paulh002/ESP32vfo/ESP32vfo/FreeSansOblique24.c

/*******************************************************************************
 * Size: 24 px
 * Bpp: 1
 * Opts: 
 ******************************************************************************/

#ifdef LV_LVGL_H_INCLUDE_SIMPLE
#include "lvgl.h"
#else
#include "lvgl.h"
#endif

#ifndef FREESANSOBLIQUE24
#define FREESANSOBLIQUE24 1
#endif

#if FREESANSOBLIQUE24

/*-----------------
 *    BITMAPS
 *----------------*/

/*Store the image of the glyphs*/
static LV_ATTRIBUTE_LARGE_CONST const uint8_t glyph_bitmap[] = {
    /* U+0020 " " */
    0x0,

    /* U+002B "+" */
    0x1, 0x0, 0x30, 0x3, 0x0, 0x30, 0x2, 0xf,
    0xff, 0xff, 0xf0, 0x60, 0x6, 0x0, 0x40, 0xc,
    0x0, 0xc0,

    /* U+002C "," */
    0x77, 0x32, 0x2c,

    /* U+002D "-" */
    0x7f, 0xf0,

    /* U+002E "." */
    0xfc,

    /* U+0030 "0" */
    0x3, 0xc0, 0xfe, 0x1c, 0x71, 0x83, 0x30, 0x33,
    0x3, 0x70, 0x36, 0x3, 0x60, 0x36, 0x3, 0x60,
    0x7e, 0x6, 0xe0, 0x6c, 0xe, 0xe0, 0xc6, 0x1c,
    0x7f, 0x83, 0xf0, 0x8, 0x0,

    /* U+0031 "1" */
    0x6, 0xc, 0x33, 0xef, 0xc1, 0x83, 0xc, 0x18,
    0x30, 0x60, 0xc3, 0x6, 0xc, 0x18, 0x70, 0xc0,

    /* U+0032 "2" */
    0x3, 0xf0, 0x1f, 0xe0, 0xe1, 0x87, 0x7, 0x18,
    0xc, 0x60, 0x30, 0x1, 0x80, 0xe, 0x0, 0x70,
    0x7, 0x80, 0x3c, 0x3, 0xc0, 0x1c, 0x0, 0xe0,
    0x6, 0x0, 0x18, 0x0, 0xff, 0xe3, 0xff, 0x80,

    /* U+0033 "3" */
    0x7, 0xc0, 0xff, 0x1c, 0x73, 0x83, 0x30, 0x33,
    0x3, 0x0, 0x30, 0xe, 0x7, 0xc0, 0x7c, 0x0,
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
    0x0, 0xc0, 0x6, 0x0, 0xf8, 0x3, 0x80, 0x0,

    /* U+007A "z" */
    0x1f, 0xf1, 0xff, 0x0, 0x60, 0xc, 0x1, 0x80,
    0x30, 0x6, 0x0, 0xc0, 0x18, 0x3, 0x0, 0x60,
    0xf, 0xfc, 0xff, 0xc0
};


/*---------------------
 *  GLYPH DESCRIPTION
 *--------------------*/

static const lv_font_fmt_txt_glyph_dsc_t glyph_dsc[] = {
    {.bitmap_index = 0, .adv_w = 0, .box_w = 0, .box_h = 0, .ofs_x = 0, .ofs_y = 0} /* id = 0 reserved */,
    {.bitmap_index = 0, .adv_w = 107, .box_w = 1, .box_h = 1, .ofs_x = 0, .ofs_y = 0},
    {.bitmap_index = 1, .adv_w = 224, .box_w = 12, .box_h = 12, .ofs_x = 2, .ofs_y = 0},
    {.bitmap_index = 19, .adv_w = 107, .box_w = 4, .box_h = 6, .ofs_x = 1, .ofs_y = -4},
    {.bitmap_index = 22, .adv_w = 128, .box_w = 6, .box_h = 2, .ofs_x = 2, .ofs_y = 6},
    {.bitmap_index = 24, .adv_w = 107, .box_w = 3, .box_h = 2, .ofs_x = 2, .ofs_y = 0},
    {.bitmap_index = 25, .adv_w = 214, .box_w = 12, .box_h = 19, .ofs_x = 2, .ofs_y = -1},
    {.bitmap_index = 54, .adv_w = 214, .box_w = 7, .box_h = 18, .ofs_x = 5, .ofs_y = 0},
    {.bitmap_index = 70, .adv_w = 214, .box_w = 14, .box_h = 18, .ofs_x = 1, .ofs_y = 0},
    {.bitmap_index = 102, .adv_w = 214, .box_w = 12, .box_h = 19, .ofs_x = 2, .ofs_y = -1},
    {.bitmap_index = 131, .adv_w = 214, .box_w = 12, .box_h = 18, .ofs_x = 2, .ofs_y = 0},
    {.bitmap_index = 158, .adv_w = 214, .box_w = 13, .box_h = 19, .ofs_x = 2, .ofs_y = -1},
    {.bitmap_index = 189, .adv_w = 214, .box_w = 13, .box_h = 19, .ofs_x = 2, .ofs_y = -1},
    {.bitmap_index = 220, .adv_w = 214, .box_w = 13, .box_h = 18, .ofs_x = 3, .ofs_y = 0},
    {.bitmap_index = 250, .adv_w = 214, .box_w = 13, .box_h = 19, .ofs_x = 2, .ofs_y = -1},
    {.bitmap_index = 281, .adv_w = 214, .box_w = 12, .box_h = 19, .ofs_x = 2, .ofs_y = -1},
    {.bitmap_index = 310, .adv_w = 224, .box_w = 13, .box_h = 11, .ofs_x = 2, .ofs_y = 0},
    {.bitmap_index = 328, .adv_w = 224, .box_w = 13, .box_h = 11, .ofs_x = 1, .ofs_y = 0},
    {.bitmap_index = 346, .adv_w = 214, .box_w = 11, .box_h = 18, .ofs_x = 4, .ofs_y = 0},
    {.bitmap_index = 371, .adv_w = 256, .box_w = 16, .box_h = 18, .ofs_x = 0, .ofs_y = 0},
    {.bitmap_index = 407, .adv_w = 256, .box_w = 15, .box_h = 18, .ofs_x = 2, .ofs_y = 0},
    {.bitmap_index = 441, .adv_w = 277, .box_w = 15, .box_h = 19, .ofs_x = 3, .ofs_y = -1},
    {.bitmap_index = 477, .adv_w = 277, .box_w = 16, .box_h = 18, .ofs_x = 2, .ofs_y = 0},
    {.bitmap_index = 513, .adv_w = 256, .box_w = 16, .box_h = 18, .ofs_x = 2, .ofs_y = 0},
    {.bitmap_index = 549, .adv_w = 235, .box_w = 16, .box_h = 18, .ofs_x = 2, .ofs_y = 0},
    {.bitmap_index = 585, .adv_w = 299, .box_w = 16, .box_h = 19, .ofs_x = 3, .ofs_y = -1},
    {.bitmap_index = 623, .adv_w = 277, .box_w = 17, .box_h = 18, .ofs_x = 2, .ofs_y = 0},
    {.bitmap_index = 662, .adv_w = 107, .box_w = 6, .box_h = 18, .ofs_x = 2, .ofs_y = 0},
    {.bitmap_index = 676, .adv_w = 192, .box_w = 13, .box_h = 19, .ofs_x = 1, .ofs_y = -1},
    {.bitmap_index = 707, .adv_w = 256, .box_w = 18, .box_h = 18, .ofs_x = 2, .ofs_y = 0},
    {.bitmap_index = 748, .adv_w = 214, .box_w = 11, .box_h = 18, .ofs_x = 2, .ofs_y = 0},
    {.bitmap_index = 773, .adv_w = 320, .box_w = 20, .box_h = 18, .ofs_x = 2, .ofs_y = 0},
    {.bitmap_index = 818, .adv_w = 277, .box_w = 17, .box_h = 18, .ofs_x = 2, .ofs_y = 0},
    {.bitmap_index = 857, .adv_w = 299, .box_w = 18, .box_h = 19, .ofs_x = 2, .ofs_y = -1},
    {.bitmap_index = 900, .adv_w = 256, .box_w = 16, .box_h = 18, .ofs_x = 2, .ofs_y = 0},
    {.bitmap_index = 936, .adv_w = 299, .box_w = 18, .box_h = 19, .ofs_x = 2, .ofs_y = -1},
    {.bitmap_index = 979, .adv_w = 277, .box_w = 16, .box_h = 18, .ofs_x = 2, .ofs_y = 0},
    {.bitmap_index = 1015, .adv_w = 256, .box_w = 15, .box_h = 19, .ofs_x = 2, .ofs_y = -1},
    {.bitmap_index = 1051, .adv_w = 235, .box_w = 14, .box_h = 18, .ofs_x = 4, .ofs_y = 0},
    {.bitmap_index = 1083, .adv_w = 277, .box_w = 16, .box_h = 19, .ofs_x = 3, .ofs_y = -1},
    {.bitmap_index = 1121, .adv_w = 256, .box_w = 15, .box_h = 18, .ofs_x = 4, .ofs_y = 0},
    {.bitmap_index = 1155, .adv_w = 362, .box_w = 22, .box_h = 18, .ofs_x = 4, .ofs_y = 0},
    {.bitmap_index = 1205, .adv_w = 256, .box_w = 18, .box_h = 18, .ofs_x = 1, .ofs_y = 0},
    {.bitmap_index = 1246, .adv_w = 256, .box_w = 16, .box_h = 18, .ofs_x = 4, .ofs_y = 0},
    {.bitmap_index = 1282, .adv_w = 235, .box_w = 17, .box_h = 18, .ofs_x = 1, .ofs_y = 0},
    {.bitmap_index = 1321, .adv_w = 107, .box_w = 10, .box_h = 23, .ofs_x = 0, .ofs_y = -5},
    {.bitmap_index = 1350, .adv_w = 107, .box_w = 10, .box_h = 23, .ofs_x = -1, .ofs_y = -5},
    {.bitmap_index = 1379, .adv_w = 214, .box_w = 12, .box_h = 14, .ofs_x = 2, .ofs_y = -1},
    {.bitmap_index = 1400, .adv_w = 214, .box_w = 13, .box_h = 19, .ofs_x = 1, .ofs_y = -1},
    {.bitmap_index = 1431, .adv_w = 192, .box_w = 11, .box_h = 14, .ofs_x = 2, .ofs_y = -1},
    {.bitmap_index = 1451, .adv_w = 214, .box_w = 14, .box_h = 19, .ofs_x = 2, .ofs_y = -1},
    {.bitmap_index = 1485, .adv_w = 214, .box_w = 12, .box_h = 14, .ofs_x = 2, .ofs_y = -1},
    {.bitmap_index = 1506, .adv_w = 107, .box_w = 8, .box_h = 18, .ofs_x = 2, .ofs_y = 0},
    {.bitmap_index = 1524, .adv_w = 214, .box_w = 13, .box_h = 18, .ofs_x = 1, .ofs_y = -5},
    {.bitmap_index = 1554, .adv_w = 214, .box_w = 12, .box_h = 18, .ofs_x = 2, .ofs_y = 0},
    {.bitmap_index = 1581, .adv_w = 85, .box_w = 5, .box_h = 18, .ofs_x = 2, .ofs_y = 0},
    {.bitmap_index = 1593, .adv_w = 85, .box_w = 9, .box_h = 23, .ofs_x = -2, .ofs_y = -5},
    {.bitmap_index = 1619, .adv_w = 192, .box_w = 13, .box_h = 18, .ofs_x = 1, .ofs_y = 0},
    {.bitmap_index = 1649, .adv_w = 85, .box_w = 5, .box_h = 18, .ofs_x = 2, .ofs_y = 0},
    {.bitmap_index = 1661, .adv_w = 320, .box_w = 18, .box_h = 13, .ofs_x = 2, .ofs_y = 0},
    {.bitmap_index = 1691, .adv_w = 214, .box_w = 12, .box_h = 13, .ofs_x = 2, .ofs_y = 0},
    {.bitmap_index = 1711, .adv_w = 214, .box_w = 12, .box_h = 14, .ofs_x = 2, .ofs_y = -1},
    {.bitmap_index = 1732, .adv_w = 214, .box_w = 14, .box_h = 18, .ofs_x = 0, .ofs_y = -5},
    {.bitmap_index = 1764, .adv_w = 214, .box_w = 13, .box_h = 18, .ofs_x = 2, .ofs_y = -5},
    {.bitmap_index = 1794, .adv_w = 128, .box_w = 8, .box_h = 13, .ofs_x = 2, .ofs_y = 0},
    {.bitmap_index = 1807, .adv_w = 192, .box_w = 11, .box_h = 14, .ofs_x = 1, .ofs_y = -1},
    {.bitmap_index = 1827, .adv_w = 107, .box_w = 7, .box_h = 17, .ofs_x = 2, .ofs_y = -1},
    {.bitmap_index = 1842, .adv_w = 214, .box_w = 12, .box_h = 14, .ofs_x = 2, .ofs_y = -1},
    {.bitmap_index = 1863, .adv_w = 192, .box_w = 11, .box_h = 13, .ofs_x = 3, .ofs_y = 0},
    {.bitmap_index = 1881, .adv_w = 277, .box_w = 17, .box_h = 13, .ofs_x = 3, .ofs_y = 0},
    {.bitmap_index = 1909, .adv_w = 192, .box_w = 14, .box_h = 13, .ofs_x = 0, .ofs_y = 0},
    {.bitmap_index = 1932, .adv_w = 192, .box_w = 14, .box_h = 18, .ofs_x = 0, .ofs_y = -5},
    {.bitmap_index = 1964, .adv_w = 192, .box_w = 12, .box_h = 13, .ofs_x = 1, .ofs_y = 0}
};

/*---------------------
 *  CHARACTER MAPPING
 *--------------------*/

static const uint8_t glyph_id_ofs_list_0[] = {
    0, 0, 0, 0, 0, 0, 0, 0,
    0, 0, 0, 1, 2, 3, 4, 0,
    5, 6, 7, 8, 9, 10, 11, 12,
    13, 14, 0, 0, 15, 0, 16, 17,
    0, 18, 19, 20, 21, 22, 23, 24,
    25, 26, 27, 28, 29, 30, 31, 32,
    33, 34, 35, 36, 37, 38, 39, 40,
    41, 42, 43, 44, 0, 45
};

/*Collect the unicode lists and glyph_id offsets*/
static const lv_font_fmt_txt_cmap_t cmaps[] =
{
    {
        .range_start = 32, .range_length = 62, .glyph_id_start = 1,
        .unicode_list = NULL, .glyph_id_ofs_list = glyph_id_ofs_list_0, .list_length = 62, .type = LV_FONT_FMT_TXT_CMAP_FORMAT0_FULL
    },
    {
        .range_start = 97, .range_length = 26, .glyph_id_start = 47,
        .unicode_list = NULL, .glyph_id_ofs_list = NULL, .list_length = 0, .type = LV_FONT_FMT_TXT_CMAP_FORMAT0_TINY
    }
};

/*-----------------
 *    KERNING
 *----------------*/


/*Map glyph_ids to kern left classes*/
static const uint8_t kern_left_class_mapping[] =
{
    0, 0, 0, 0, 1, 0, 0, 0,
    0, 0, 0, 0, 0, 0, 0, 0,
    0, 0, 0, 2, 3, 4, 4, 5,
    6, 4, 0, 0, 7, 8, 9, 0,
    0, 10, 11, 10, 12, 13, 14, 0,
    15, 15, 8, 15, 8, 0, 0, 16,
    17, 17, 0, 17, 18, 0, 19, 0,
    0, 20, 0, 19, 19, 17, 17, 0,
    21, 22, 23, 0, 24, 24, 20, 24,
    25
};

/*Map glyph_ids to kern right classes*/
static const uint8_t kern_right_class_mapping[] =
{
    0, 0, 0, 0, 0, 0, 0, 0,
    0, 0, 0, 0, 0, 0, 0, 0,
    0, 0, 0, 1, 0, 2, 0, 0,
    0, 2, 0, 0, 3, 0, 0, 0,
    0, 2, 0, 2, 0, 4, 5, 0,
    6, 6, 7, 6, 7, 0, 0, 8,
    0, 9, 9, 9, 10, 8, 0, 0,
    11, 0, 0, 12, 12, 9, 13, 9,
    14, 15, 10, 16, 17, 17, 18, 17,
    12
};

/*Kern values between classes*/
static const int8_t kern_class_values[] =
{
    -23, -8, -8, -23, -19, -23, -23, -15,
    0, -19, -12, -15, -15, -15, -19, -15,
    -23, -23, 0, -15, 0, -12, -15, -23,
    -4, -8, -8, -12, 0, -12, -8, -12,
    -8, -10, -12, 0, -12, -12, 0, -8,
    -19, -19, -19, -4, 0, -4, -8, -12,
    -4, -8, -4, -8, -12, -12, -15, -8,
    0, -4, -15, -19, -15, -8, 0, -8,
    -12, -12, -8, -8, -8, -12, -4, -12,
    -12, -15, -8, -19, -8, -19, -12, -12,
    -12, -12, -12, -15, -8, -12, -8, -17,
    -15, -12, -15, -12, -12, -15, 0, -8,
    -12, -12, -12, -8, -8, -19, -12, -15,
    -15, -19, -4, -15, -12, -12, 0, -12,
    0, -19, -19, -12, -8, 0, -8, -15,
    -8, -12, -8, -15, -12, -19, 0, -19,
    0, -19, 0, 0, 0, -12, -15, -12,
    -4, -15, -12, -15, -8, -15, -12, -8,
    0, -15, 0, -15, -15, -23, 0, -8,
    -12, -12, -4, -15, 0, -12, -8, -15,
    -15, 0, -12, 0, 0, -8, -15, -15,
    -19, -8, 0, 0, 0, -8, -4, -8,
    0, -6, 0, 0, -23, -8, -15, -12,
    -12, -15, -23, -19, -15, 0, 0, -15,
    -8, -12, -12, -15, 0, -15, -4, -4,
    0, -8, -8, -19, -8, -4, -4, 0,
    -4, -4, -4, -8, -4, -15, -4, 0,
    -12, -8, 0, -4, -15, -19, -19, 0,
    0, -4, -4, -8, -4, -8, 0, -10,
    -8, -15, -19, -15, -15, -15, 0, -4,
    -15, -15, -15, -8, 0, -15, -12, -15,
    -15, -15, -8, -12, -23, -19, -12, -19,
    0, 0, -12, -19, -19, -8, 0, -23,
    -15, -23, -15, -19, 0, -12, 0, 0,
    0, 0, 0, 0, 0, -4, 0, -4,
    0, -4, 0, -4, -4, -4, -8, -4,
    0, 0, 0, 0, 0, 0, 0, 0,
    0, -4, 0, -4, 0, -4, -4, -2,
    -4, -8, 0, 0, 0, 0, 0, 0,
    0, -8, -8, 0, 0, -4, 0, -4,
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
};


/*Collect the kern class' data in one place*/
static const lv_font_fmt_txt_kern_classes_t kern_classes =
{
    .class_pair_values   = kern_class_values,
    .left_class_mapping  = kern_left_class_mapping,
    .right_class_mapping = kern_right_class_mapping,
    .left_class_cnt      = 25,
    .right_class_cnt     = 18,
};

/*--------------------
 *  ALL CUSTOM DATA
 *--------------------*/

#if LV_VERSION_CHECK(8, 0, 0)
/*Store all the custom data of the font*/
static  lv_font_fmt_txt_glyph_cache_t cache;
static const lv_font_fmt_txt_dsc_t font_dsc = {
#else
static lv_font_fmt_txt_dsc_t font_dsc = {
#endif
    .glyph_bitmap = glyph_bitmap,
    .glyph_dsc = glyph_dsc,
    .cmaps = cmaps,
    .kern_dsc = &kern_classes,
    .kern_scale = 16,
    .cmap_num = 2,
    .bpp = 1,
    .kern_classes = 1,
    .bitmap_format = 0,
#if LV_VERSION_CHECK(8, 0, 0)
    .cache = &cache
#endif
};


/*-----------------
 *  PUBLIC FONT
 *----------------*/

/*Initialize a public general font descriptor*/
#if LV_VERSION_CHECK(8, 0, 0)
const lv_font_t FreeSansOblique24 = {
#else
lv_font_t FreeSansOblique24 = {
#endif
    .get_glyph_dsc = lv_font_get_glyph_dsc_fmt_txt,    /*Function pointer to get glyph's data*/
    .get_glyph_bitmap = lv_font_get_bitmap_fmt_txt,    /*Function pointer to get glyph's bitmap*/
    .line_height = 23,          /*The maximum line height required by the font*/
    .base_line = 5,             /*Baseline measured from the bottom of the line*/
#if !(LVGL_VERSION_MAJOR == 6 && LVGL_VERSION_MINOR == 0)
    .subpx = LV_FONT_SUBPX_NONE,
#endif
#if LV_VERSION_CHECK(7, 4, 0)
    .underline_position = -4,
    .underline_thickness = 1,
#endif
    .dsc = &font_dsc           /*The custom font data. Will be accessed by `get_glyph_bitmap/dsc` */
};



#endif /*#if FREESANSOBLIQUE24*/
