paulh002/ESP32vfo/ESP32vfo/FreeSansOblique42.c

/*******************************************************************************
 * Size: 42 px
 * Bpp: 1
 * Opts: 
 ******************************************************************************/

#ifdef LV_LVGL_H_INCLUDE_SIMPLE
#include "lvgl.h"
#else
#include "lvgl.h"
#endif

#ifndef FREESANSOBLIQUE42
#define FREESANSOBLIQUE42 1
#endif

#if FREESANSOBLIQUE42

/*-----------------
 *    BITMAPS
 *----------------*/

/*Store the image of the glyphs*/
static LV_ATTRIBUTE_LARGE_CONST const uint8_t glyph_bitmap[] = {
    /* U+0020 " " */
    0x0,

    /* U+002B "+" */
    0x0, 0x1c, 0x0, 0x0, 0xe0, 0x0, 0x6, 0x0,
    0x0, 0x70, 0x0, 0x3, 0x80, 0x0, 0x1c, 0x0,
    0x0, 0xe0, 0x0, 0xe, 0x0, 0x0, 0x70, 0x7,
    0xff, 0xff, 0xff, 0xff, 0xff, 0xff, 0xff, 0xe0,
    0xe, 0x0, 0x0, 0x70, 0x0, 0x3, 0x80, 0x0,
    0x1c, 0x0, 0x0, 0xe0, 0x0, 0xe, 0x0, 0x0,
    0x70, 0x0, 0x3, 0x80, 0x0, 0x1c, 0x0, 0x0,

    /* U+002C "," */
    0x3e, 0x7c, 0xf1, 0xe0, 0xc1, 0x82, 0xc, 0x31,
    0xc0,

    /* U+002D "-" */
    0x7f, 0xff, 0xfb, 0xff, 0x0,

    /* U+002E "." */
    0xff, 0xfd, 0xe0,

    /* U+0030 "0" */
    0x0, 0x1f, 0x80, 0x7, 0xfe, 0x0, 0x7f, 0xf8,
    0x7, 0xc3, 0xe0, 0x78, 0xf, 0x83, 0x80, 0x3c,
    0x3c, 0x1, 0xe3, 0xc0, 0xf, 0x1e, 0x0, 0x78,
    0xe0, 0x3, 0xcf, 0x0, 0x1e, 0x78, 0x0, 0xf3,
    0x80, 0x7, 0xbc, 0x0, 0x3d, 0xe0, 0x1, 0xef,
    0x0, 0xe, 0x70, 0x0, 0xf3, 0x80, 0x7, 0xbc,
    0x0, 0x3d, 0xe0, 0x1, 0xcf, 0x0, 0x1e, 0x78,
    0x0, 0xf3, 0xc0, 0xf, 0x1e, 0x0, 0x78, 0xf0,
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
    0x0, 0x0, 0x78, 0x0, 0x3, 0xc0, 0x0, 0x1e,
    0x0, 0x0, 0xf0, 0x0, 0x7, 0x80, 0x0, 0x3c,
    0x0, 0x1, 0xe0, 0x0, 0xf, 0x0, 0x0, 0xf8,
    0x0, 0x7, 0xc0, 0x0, 0x1f, 0xff, 0xf8, 0x7f,
    0xff, 0xe3, 0xff, 0xff, 0x0
};


/*---------------------
 *  GLYPH DESCRIPTION
 *--------------------*/

static const lv_font_fmt_txt_glyph_dsc_t glyph_dsc[] = {
    {.bitmap_index = 0, .adv_w = 0, .box_w = 0, .box_h = 0, .ofs_x = 0, .ofs_y = 0} /* id = 0 reserved */,
    {.bitmap_index = 0, .adv_w = 187, .box_w = 1, .box_h = 1, .ofs_x = 0, .ofs_y = 0},
    {.bitmap_index = 1, .adv_w = 392, .box_w = 21, .box_h = 21, .ofs_x = 4, .ofs_y = -1},
    {.bitmap_index = 57, .adv_w = 187, .box_w = 7, .box_h = 10, .ofs_x = 2, .ofs_y = -6},
    {.bitmap_index = 66, .adv_w = 224, .box_w = 11, .box_h = 3, .ofs_x = 4, .ofs_y = 10},
    {.bitmap_index = 71, .adv_w = 187, .box_w = 5, .box_h = 4, .ofs_x = 4, .ofs_y = 0},
    {.bitmap_index = 74, .adv_w = 374, .box_w = 21, .box_h = 31, .ofs_x = 4, .ofs_y = -1},
    {.bitmap_index = 156, .adv_w = 374, .box_w = 12, .box_h = 31, .ofs_x = 9, .ofs_y = 0},
    {.bitmap_index = 203, .adv_w = 374, .box_w = 25, .box_h = 30, .ofs_x = 1, .ofs_y = 0},
    {.bitmap_index = 297, .adv_w = 374, .box_w = 22, .box_h = 31, .ofs_x = 3, .ofs_y = -1},
    {.bitmap_index = 383, .adv_w = 374, .box_w = 21, .box_h = 30, .ofs_x = 3, .ofs_y = 0},
    {.bitmap_index = 462, .adv_w = 374, .box_w = 23, .box_h = 31, .ofs_x = 3, .ofs_y = -1},
    {.bitmap_index = 552, .adv_w = 374, .box_w = 22, .box_h = 31, .ofs_x = 4, .ofs_y = -1},
    {.bitmap_index = 638, .adv_w = 374, .box_w = 22, .box_h = 30, .ofs_x = 6, .ofs_y = 0},
    {.bitmap_index = 721, .adv_w = 374, .box_w = 22, .box_h = 31, .ofs_x = 3, .ofs_y = -1},
    {.bitmap_index = 807, .adv_w = 374, .box_w = 22, .box_h = 31, .ofs_x = 3, .ofs_y = -1},
    {.bitmap_index = 893, .adv_w = 392, .box_w = 23, .box_h = 20, .ofs_x = 4, .ofs_y = 0},
    {.bitmap_index = 951, .adv_w = 392, .box_w = 23, .box_h = 20, .ofs_x = 2, .ofs_y = 0},
    {.bitmap_index = 1009, .adv_w = 374, .box_w = 18, .box_h = 31, .ofs_x = 8, .ofs_y = 0},
    {.bitmap_index = 1079, .adv_w = 448, .box_w = 26, .box_h = 31, .ofs_x = 1, .ofs_y = 0},
    {.bitmap_index = 1180, .adv_w = 448, .box_w = 27, .box_h = 30, .ofs_x = 3, .ofs_y = 1},
    {.bitmap_index = 1282, .adv_w = 485, .box_w = 27, .box_h = 32, .ofs_x = 5, .ofs_y = -1},
    {.bitmap_index = 1390, .adv_w = 485, .box_w = 28, .box_h = 30, .ofs_x = 4, .ofs_y = 1},
    {.bitmap_index = 1495, .adv_w = 448, .box_w = 28, .box_h = 30, .ofs_x = 4, .ofs_y = 1},
    {.bitmap_index = 1600, .adv_w = 411, .box_w = 27, .box_h = 31, .ofs_x = 4, .ofs_y = 0},
    {.bitmap_index = 1705, .adv_w = 523, .box_w = 29, .box_h = 32, .ofs_x = 5, .ofs_y = -1},
    {.bitmap_index = 1821, .adv_w = 485, .box_w = 31, .box_h = 31, .ofs_x = 3, .ofs_y = 0},
    {.bitmap_index = 1942, .adv_w = 187, .box_w = 11, .box_h = 31, .ofs_x = 4, .ofs_y = 0},
    {.bitmap_index = 1985, .adv_w = 336, .box_w = 22, .box_h = 32, .ofs_x = 2, .ofs_y = -1},
    {.bitmap_index = 2073, .adv_w = 448, .box_w = 31, .box_h = 31, .ofs_x = 3, .ofs_y = 0},
    {.bitmap_index = 2194, .adv_w = 374, .box_w = 20, .box_h = 31, .ofs_x = 3, .ofs_y = 0},
    {.bitmap_index = 2272, .adv_w = 560, .box_w = 35, .box_h = 31, .ofs_x = 3, .ofs_y = 0},
    {.bitmap_index = 2408, .adv_w = 485, .box_w = 31, .box_h = 31, .ofs_x = 3, .ofs_y = 0},
    {.bitmap_index = 2529, .adv_w = 523, .box_w = 31, .box_h = 32, .ofs_x = 4, .ofs_y = -1},
    {.bitmap_index = 2653, .adv_w = 448, .box_w = 27, .box_h = 31, .ofs_x = 4, .ofs_y = 0},
    {.bitmap_index = 2758, .adv_w = 523, .box_w = 31, .box_h = 34, .ofs_x = 4, .ofs_y = -3},
    {.bitmap_index = 2890, .adv_w = 485, .box_w = 28, .box_h = 31, .ofs_x = 4, .ofs_y = 0},
    {.bitmap_index = 2999, .adv_w = 448, .box_w = 26, .box_h = 32, .ofs_x = 4, .ofs_y = -1},
    {.bitmap_index = 3103, .adv_w = 411, .box_w = 24, .box_h = 31, .ofs_x = 7, .ofs_y = 0},
    {.bitmap_index = 3196, .adv_w = 485, .box_w = 29, .box_h = 32, .ofs_x = 5, .ofs_y = -1},
    {.bitmap_index = 3312, .adv_w = 448, .box_w = 26, .box_h = 31, .ofs_x = 8, .ofs_y = 0},
    {.bitmap_index = 3413, .adv_w = 634, .box_w = 39, .box_h = 31, .ofs_x = 7, .ofs_y = 0},
    {.bitmap_index = 3565, .adv_w = 448, .box_w = 32, .box_h = 31, .ofs_x = 1, .ofs_y = 0},
    {.bitmap_index = 3689, .adv_w = 448, .box_w = 27, .box_h = 31, .ofs_x = 7, .ofs_y = 0},
    {.bitmap_index = 3794, .adv_w = 411, .box_w = 30, .box_h = 30, .ofs_x = 1, .ofs_y = 1},
    {.bitmap_index = 3907, .adv_w = 187, .box_w = 16, .box_h = 40, .ofs_x = 1, .ofs_y = -9},
    {.bitmap_index = 3987, .adv_w = 187, .box_w = 16, .box_h = 40, .ofs_x = -1, .ofs_y = -9},
    {.bitmap_index = 4067, .adv_w = 374, .box_w = 21, .box_h = 24, .ofs_x = 3, .ofs_y = -1},
    {.bitmap_index = 4130, .adv_w = 374, .box_w = 23, .box_h = 32, .ofs_x = 2, .ofs_y = -1},
    {.bitmap_index = 4222, .adv_w = 336, .box_w = 20, .box_h = 24, .ofs_x = 3, .ofs_y = -1},
    {.bitmap_index = 4282, .adv_w = 374, .box_w = 24, .box_h = 32, .ofs_x = 3, .ofs_y = -1},
    {.bitmap_index = 4378, .adv_w = 374, .box_w = 20, .box_h = 24, .ofs_x = 4, .ofs_y = -1},
    {.bitmap_index = 4438, .adv_w = 187, .box_w = 13, .box_h = 32, .ofs_x = 4, .ofs_y = -1},
    {.bitmap_index = 4490, .adv_w = 374, .box_w = 24, .box_h = 32, .ofs_x = 1, .ofs_y = -9},
    {.bitmap_index = 4586, .adv_w = 374, .box_w = 21, .box_h = 32, .ofs_x = 3, .ofs_y = -1},
    {.bitmap_index = 4670, .adv_w = 149, .box_w = 10, .box_h = 32, .ofs_x = 3, .ofs_y = -1},
    {.bitmap_index = 4710, .adv_w = 149, .box_w = 16, .box_h = 40, .ofs_x = -3, .ofs_y = -9},
    {.bitmap_index = 4790, .adv_w = 336, .box_w = 23, .box_h = 31, .ofs_x = 2, .ofs_y = 0},
    {.bitmap_index = 4880, .adv_w = 149, .box_w = 10, .box_h = 31, .ofs_x = 3, .ofs_y = 0},
    {.bitmap_index = 4919, .adv_w = 560, .box_w = 33, .box_h = 24, .ofs_x = 3, .ofs_y = -1},
    {.bitmap_index = 5018, .adv_w = 374, .box_w = 21, .box_h = 24, .ofs_x = 3, .ofs_y = -1},
    {.bitmap_index = 5081, .adv_w = 374, .box_w = 21, .box_h = 24, .ofs_x = 3, .ofs_y = -1},
    {.bitmap_index = 5144, .adv_w = 374, .box_w = 25, .box_h = 32, .ofs_x = 0, .ofs_y = -9},
    {.bitmap_index = 5244, .adv_w = 374, .box_w = 23, .box_h = 32, .ofs_x = 3, .ofs_y = -9},
    {.bitmap_index = 5336, .adv_w = 224, .box_w = 15, .box_h = 24, .ofs_x = 3, .ofs_y = -1},
    {.bitmap_index = 5381, .adv_w = 336, .box_w = 19, .box_h = 24, .ofs_x = 3, .ofs_y = -1},
    {.bitmap_index = 5438, .adv_w = 187, .box_w = 11, .box_h = 29, .ofs_x = 4, .ofs_y = -1},
    {.bitmap_index = 5478, .adv_w = 374, .box_w = 21, .box_h = 23, .ofs_x = 4, .ofs_y = -1},
    {.bitmap_index = 5539, .adv_w = 336, .box_w = 20, .box_h = 22, .ofs_x = 5, .ofs_y = 0},
    {.bitmap_index = 5594, .adv_w = 485, .box_w = 29, .box_h = 22, .ofs_x = 5, .ofs_y = 0},
    {.bitmap_index = 5674, .adv_w = 336, .box_w = 23, .box_h = 23, .ofs_x = 1, .ofs_y = -1},
    {.bitmap_index = 5741, .adv_w = 336, .box_w = 25, .box_h = 31, .ofs_x = 0, .ofs_y = -9},
    {.bitmap_index = 5838, .adv_w = 336, .box_w = 22, .box_h = 22, .ofs_x = 1, .ofs_y = 0}
};

/*---------------------
 *  CHARACTER MAPPING
 *--------------------*/

static const uint8_t glyph_id_ofs_list_0[] = {
    0, 0, 0, 0, 0, 0, 0, 0,
    0, 0, 0, 1, 2, 3, 4, 0,
    5, 6, 7, 8, 9, 10, 11, 12,
    13, 14, 0, 0, 15, 0, 16, 17,
    0, 18, 19, 20, 21, 22, 23, 24,
    25, 26, 27, 28, 29, 30, 31, 32,
    33, 34, 35, 36, 37, 38, 39, 40,
    41, 42, 43, 44, 0, 45
};

/*Collect the unicode lists and glyph_id offsets*/
static const lv_font_fmt_txt_cmap_t cmaps[] =
{
    {
        .range_start = 32, .range_length = 62, .glyph_id_start = 1,
        .unicode_list = NULL, .glyph_id_ofs_list = glyph_id_ofs_list_0, .list_length = 62, .type = LV_FONT_FMT_TXT_CMAP_FORMAT0_FULL
    },
    {
        .range_start = 97, .range_length = 26, .glyph_id_start = 47,
        .unicode_list = NULL, .glyph_id_ofs_list = NULL, .list_length = 0, .type = LV_FONT_FMT_TXT_CMAP_FORMAT0_TINY
    }
};

/*-----------------
 *    KERNING
 *----------------*/


/*Map glyph_ids to kern left classes*/
static const uint8_t kern_left_class_mapping[] =
{
    0, 0, 0, 0, 1, 0, 0, 0,
    0, 0, 0, 0, 0, 0, 0, 0,
    0, 0, 0, 2, 3, 4, 4, 5,
    6, 4, 0, 0, 7, 8, 9, 0,
    0, 10, 11, 10, 12, 13, 14, 0,
    15, 15, 8, 15, 8, 0, 0, 16,
    17, 17, 0, 17, 18, 0, 19, 0,
    0, 20, 0, 19, 19, 17, 17, 0,
    21, 22, 23, 0, 24, 24, 20, 24,
    25
};

/*Map glyph_ids to kern right classes*/
static const uint8_t kern_right_class_mapping[] =
{
    0, 0, 0, 0, 0, 0, 0, 0,
    0, 0, 0, 0, 0, 0, 0, 0,
    0, 0, 0, 1, 0, 2, 0, 0,
    0, 2, 0, 0, 3, 0, 0, 0,
    0, 2, 0, 2, 0, 4, 5, 0,
    6, 6, 7, 6, 7, 0, 0, 8,
    0, 9, 9, 9, 10, 8, 0, 0,
    11, 0, 0, 12, 12, 9, 13, 9,
    14, 15, 10, 16, 17, 17, 18, 17,
    12
};

/*Kern values between classes*/
static const int8_t kern_class_values[] =
{
    -40, -13, -13, -40, -34, -40, -40, -27,
    0, -34, -20, -27, -27, -27, -34, -27,
    -40, -40, 0, -27, 0, -20, -27, -40,
    -7, -13, -13, -20, 0, -20, -13, -20,
    -13, -17, -20, 0, -20, -20, 0, -13,
    -34, -34, -34, -7, 0, -7, -13, -20,
    -7, -13, -7, -13, -20, -20, -27, -13,
    0, -7, -27, -34, -27, -13, 0, -13,
    -20, -20, -13, -13, -13, -20, -7, -20,
    -20, -27, -13, -34, -13, -34, -20, -20,
    -20, -20, -20, -27, -13, -20, -13, -30,
    -27, -20, -27, -20, -20, -27, 0, -13,
    -20, -20, -20, -13, -13, -34, -20, -27,
    -27, -34, -7, -27, -20, -20, 0, -20,
    0, -34, -34, -20, -13, 0, -13, -27,
    -13, -20, -13, -27, -20, -34, 0, -34,
    0, -34, 0, 0, 0, -20, -27, -20,
    -7, -27, -20, -27, -13, -27, -20, -13,
    0, -27, 0, -27, -27, -40, 0, -13,
    -20, -20, -7, -27, 0, -20, -13, -27,
    -27, 0, -20, 0, 0, -13, -27, -27,
    -34, -13, 0, 0, 0, -13, -7, -13,
    0, -10, 0, 0, -40, -13, -27, -20,
    -20, -27, -40, -34, -27, 0, 0, -27,
    -13, -20, -20, -27, 0, -27, -7, -7,
    0, -13, -13, -34, -13, -7, -7, 0,
    -7, -7, -7, -13, -7, -27, -7, 0,
    -20, -13, 0, -7, -27, -34, -34, 0,
    0, -7, -7, -13, -7, -13, 0, -17,
    -13, -27, -34, -27, -27, -27, 0, -7,
    -27, -27, -27, -13, 0, -27, -20, -27,
    -27, -27, -13, -20, -40, -34, -20, -34,
    0, 0, -20, -34, -34, -13, 0, -40,
    -27, -40, -27, -34, 0, -20, 0, 0,
    0, 0, 0, 0, 0, -7, 0, -7,
    0, -7, 0, -7, -7, -7, -13, -7,
    0, 0, 0, 0, 0, 0, 0, 0,
    0, -7, 0, -7, 0, -7, -7, -3,
    -7, -13, 0, 0, 0, 0, 0, 0,
    0, -13, -13, 0, 0, -7, 0, -7,
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
};


/*Collect the kern class' data in one place*/
static const lv_font_fmt_txt_kern_classes_t kern_classes =
{
    .class_pair_values   = kern_class_values,
    .left_class_mapping  = kern_left_class_mapping,
    .right_class_mapping = kern_right_class_mapping,
    .left_class_cnt      = 25,
    .right_class_cnt     = 18,
};

/*--------------------
 *  ALL CUSTOM DATA
 *--------------------*/

#if LV_VERSION_CHECK(8, 0, 0)
/*Store all the custom data of the font*/
static  lv_font_fmt_txt_glyph_cache_t cache;
static const lv_font_fmt_txt_dsc_t font_dsc = {
#else
static lv_font_fmt_txt_dsc_t font_dsc = {
#endif
    .glyph_bitmap = glyph_bitmap,
    .glyph_dsc = glyph_dsc,
    .cmaps = cmaps,
    .kern_dsc = &kern_classes,
    .kern_scale = 16,
    .cmap_num = 2,
    .bpp = 1,
    .kern_classes = 1,
    .bitmap_format = 0,
#if LV_VERSION_CHECK(8, 0, 0)
    .cache = &cache
#endif
};


/*-----------------
 *  PUBLIC FONT
 *----------------*/

/*Initialize a public general font descriptor*/
#if LV_VERSION_CHECK(8, 0, 0)
const lv_font_t FreeSansOblique42 = {
#else
lv_font_t FreeSansOblique42 = {
#endif
    .get_glyph_dsc = lv_font_get_glyph_dsc_fmt_txt,    /*Function pointer to get glyph's data*/
    .get_glyph_bitmap = lv_font_get_bitmap_fmt_txt,    /*Function pointer to get glyph's bitmap*/
    .line_height = 40,          /*The maximum line height required by the font*/
    .base_line = 9,             /*Baseline measured from the bottom of the line*/
#if !(LVGL_VERSION_MAJOR == 6 && LVGL_VERSION_MINOR == 0)
    .subpx = LV_FONT_SUBPX_NONE,
#endif
#if LV_VERSION_CHECK(7, 4, 0)
    .underline_position = -7,
    .underline_thickness = 2,
#endif
    .dsc = &font_dsc           /*The custom font data. Will be accessed by `get_glyph_bitmap/dsc` */
};



#endif /*#if FREESANSOBLIQUE42*/
