paulh002/ESP32vfo/ESP32vfo/ui_img_indicator_hor_png.c

// SquareLine LVGL GENERATED FILE
// EDITOR VERSION: SquareLine Studio 1.1.1
// LVGL VERSION: 8.3.3
// PROJECT: SquareLine_Project

#include <lvgl.h>

#ifndef LV_ATTRIBUTE_MEM_ALIGN
    #define LV_ATTRIBUTE_MEM_ALIGN
#endif

// IMAGE DATA: assets\indicator_hor.png
const LV_ATTRIBUTE_MEM_ALIGN uint8_t ui_img_indicator_hor_png_data[] = {
    0xEF, 0x57, 0x00, 0xEF, 0x57, 0x55, 0xEF, 0x57, 0xD4, 0xEF, 0x57, 0xF9, 0xEF, 0x57, 0xD4, 0xEF, 0x57, 0x54, 0xEF, 0x57, 0x00, 0xEF, 0x57, 0x00, 0xEF, 0x57, 0x00, 0xEF, 0x57, 0x00, 0xEF, 0x57, 0x00, 0xEF, 0x57, 0x55, 0xEF, 0x57, 0xD4, 0xEF, 0x57, 0xF9, 0xEF, 0x57, 0xD4, 0xEF, 0x57, 0x54, 0xEF, 0x57, 0x00, 0xEF, 0x57, 0x00, 0xEF, 0x57, 0x00, 0xEF, 0x57, 0x00, 0xEF, 0x57, 0x00, 0xEF, 0x57, 0x55, 0xEF, 0x57, 0xD4, 0xEF, 0x57, 0xF9, 0xEF, 0x57, 0xD4, 0xEF, 0x57, 0x54, 0xEF, 0x57, 0x00, 0xEF, 0x57, 0x00, 0xEF, 0x57, 0x00, 0xEF, 0x57, 0x00, 0xEF, 0x57, 0x00, 0xEF, 0x57, 0x55, 0xEF, 0x57, 0xD4, 0xEF, 0x57, 0xF9, 0xEF, 0x57, 0xD4, 0xEF, 0x57, 0x54, 0xEF, 0x57, 0x00, 0xEF, 0x57, 0x00, 0xEF, 0x57, 0x00, 0xEF, 0x57, 0x00, 0xEF, 0x57, 0x00, 0xEF, 0x57, 0x55, 0xEF, 0x57, 0xD4, 0xEF, 0x57, 0xF9, 0xEF, 0x57, 0xD4, 0xEF, 0x57, 0x54, 0xEF, 0x57, 0x00, 0xEF, 0x57, 0x00, 0xEF, 0x57, 0x00, 0xEF, 0x57, 0x00, 0xEF, 0x57, 0x00, 0xEF, 0x57, 0x55, 0xEF, 0x57, 0xD4, 0xEF, 0x57, 0xF9, 0xEF, 0x57, 0xD4, 0xEF, 0x57, 0x54, 0xEF, 0x57, 0x00, 0xEF, 0x57, 0x00, 0xEF, 0x57, 0x00, 0xEF, 0x57, 0x00, 0xEF, 0x57, 0x00, 0xEF, 0x57, 0x55, 0xEF, 0x57, 0xD4, 0xEF, 0x57, 0xF9,
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
};
const lv_img_dsc_t ui_img_indicator_hor_png = {
    .header.always_zero = 0,
    .header.w = 287,
    .header.h = 29,
    .data_size = sizeof(ui_img_indicator_hor_png_data),
    .header.cf = LV_IMG_CF_TRUE_COLOR_ALPHA,
    .data = ui_img_indicator_hor_png_data
};
